drewhirschi/daily_mirror/docs/drews-convo-with-claude-9.16.26.md

Can an esp 32 p4 run a light web server

Yes, easily. The ESP32-P4 has a dual-core RISC-V at up to 400MHz with plenty of RAM (768KB HP SRAM, plus optional PSRAM), so running a lightweight HTTP server is well within its capabilities — you could run ESP-IDF's esp_http_server component, or something like Mongoose, and serve a decent number of concurrent connections for typical IoT/local-network use cases.

One thing worth flagging: the P4 itself has no built-in WiFi or Bluetooth. Espressif paired it with the ESP32-C6 as a companion chip (communicating over SDIO) to provide connectivity — that's the setup used on the ESP32-P4 Function EV boards. So if you want the web server reachable over WiFi, you'll be using the P4 for compute and the C6 for the radio, coordinated over ESP-Hosted or a similar bridge.

If you just need Ethernet instead, the P4 has native support for that (RMII), which simplifies things since you skip the companion-chip dance entirely.

How easy would it be to write that in rust

Recalled memory
Recalled memory
Moderately easy, but with a caveat specific to the P4: it's RISC-V, and RISC-V support in the Rust ESP ecosystem is more mature than the Xtensa side, so you're actually in a better position here than you'd be on an S3 or S2.

The realistic paths:

esp-hal (no_std) + Embassy — async runtime, and someone's likely already got esp_http_server-equivalent examples or you'd wire up a minimal HTTP parser yourself over embassy-net. This is the "real embedded Rust" path: no allocator dependency by default, smaller footprint, but you're writing more of the HTTP layer yourself since the ecosystem's web server crates aren't as batteries-included as esp_http_server in C.
esp-idf-hal / esp-idf-svc (std) — Rust on top of ESP-IDF, giving you std, an allocator, threads, and direct bindings to ESP-IDF's own esp_http_server. This is the pragmatic choice if you want something working quickly: you get IDF's HTTP server for free via Rust bindings instead of hand-rolling it, at the cost of pulling in the full IDF toolchain and being less "pure Rust embedded."
Given you'd want a web server running soon rather than as a learning exercise in async embedded networking, esp-idf-svc is the faster route — it's essentially the C setup with a Rust face on it. The esp-hal/Embassy route is more idiomatic and lighter-weight but means more plumbing, especially since you'd also need to handle the P4/C6 companion-chip networking split at a lower level than IDF's WiFi abstraction handles it for you.

Worth checking current esp-hal P4 support status before committing — RISC-V support has been moving fast but P4-specific peripheral coverage (particularly around the SDIO link to the C6) may still have gaps compared to S3.

What can the c6 do as far as running a camera?

Thought for 4s
Thought for 4s
Not much, camera-wise — and this matters for how you'd architect it.

The ESP32-C6 is a connectivity-only chip: single-core RISC-V, WiFi 6, Bluetooth 5, and 802.15.4 (Thread/Zigbee). It has no DVP or MIPI-CSI camera interface at all. In the P4+C6 pairing, the C6's whole job is radio — it talks to the P4 over SDIO (via ESP-Hosted) purely to give the P4 WiFi/BT, nothing else.

Camera capture stays entirely on the P4 side. The P4 actually has solid camera support built in — both a DVP parallel interface (like the older S2/S3 camera setups) and a MIPI-CSI-2 interface, which is new for the ESP32 line and lets you use higher-resolution MIPI camera modules (like some Raspberry Pi camera sensors use) rather than being stuck with DVP-only sensors like the OV2640/OV5640 that dominate the ESP32-CAM world.

So for a P4-based camera project: P4 handles image capture and processing (and could run the ISP pipeline if you're using the CSI path), C6 just gets the resulting frames onto the network. That's a meaningfully different pipeline than the ESP32-S3 setups you'd been looking at, where the same chip does both — worth keeping in mind if you're weighing it against the S3/Arducam Mega path.

Could the c6 own its own stream raw sensor data to a backend?

No — the C6 has no camera interface (no DVP, no MIPI-CSI), so it physically can't connect to an image sensor to pull raw frame data off it. Camera sensors need those parallel/serial video interfaces to hand off pixel data at usable rates; you can't get there over the C6's available buses.

The only way raw sensor data would reach the C6 is if the P4 captures it and hands it over — at which point the C6 is just relaying data, not sourcing it. Options in that vein:

P4 captures → passes raw/compressed frames to C6 over SDIO → C6 streams to backend over WiFi. This is basically what ESP-Hosted already does implicitly for networking, but you could also treat it as an explicit data pipe if you wanted the P4 doing zero network-stack work itself, just handing frame buffers across.
P4 does everything, including WiFi via the C6 driver stack. This is the "normal" ESP-Hosted setup — C6 is invisible as a distinct actor, it's just the radio backend for the P4's network calls. Simpler, since you're not building your own inter-chip data protocol.
If you're aiming for something like "sensor talks directly to the radio chip, P4 does no camera work at all," that's not achievable on this pairing — there's no independent sensor→C6 path. The P4 has to be in the loop for capture no matter what, since it's the only chip with a camera interface.

Forget P4, what other esp32s should we look into?

Thought for 18s
Thought for 18s
You're mostly right, with one correction that matters for how you use the film.

Used the browser (7 actions) · 3 notes

Used the browser (7 actions) · 3 notes
like what do lcd panels use to even out light

Clicked, waited, opened +1
Clicked, waited, opened +1
Cart's whole again — all 9 items, and I re-added the three that silently dropped. Now your question, which is a better one than the film-vs-channel debate.

What LCDs actually do
The diffuser sheet isn't the part doing the work. The real trick is the light guide plate (LGP): a clear acrylic sheet with the LEDs firing into its edge, not its face. Light bounces along inside by total internal reflection, and a printed or etched dot pattern on the back kicks it out toward the viewer. The dots get progressively denser the farther you are from the LED edge, which is what cancels the falloff and makes the whole face read as uniform.

The full stack, back to front:

White reflector — bounces escaping light back in
Light guide plate — the even-ing happens here
Diffuser sheet — cleans up any residual dot structure
Prism film (BEF), often two layers crossed at 90° — redirects off-axis light forward, recovering a big chunk of brightness
DBEF reflective polarizer — recycles the polarization the LCD would have thrown away
That's why a phone screen is 2mm thick and perfectly even, while your strip-behind-film needs a 10–20mm air gap to look decent. Edge-lighting sidesteps the gap entirely.

Why this matters for your build
This is directly applicable, and it's arguably a better design than the ring:

Fire your COB strips into the edges of a 7×7 acrylic sheet, not at the subject. White reflector behind, diffuser on the front. You get a 7×7 panel that glows across its whole face instead of a 7×7 outline.

Same apparent width as the ring, so same softness — but roughly 3× the emitting area, so more usable light, and the reflection in glasses becomes a large dim rectangle rather than a bright thin ring. Large-and-dim is the more forgiving failure mode.

At 7 inches, you don't need a real engineered LGP. The dot-density gradient exists because a 27″ monitor has to push light a long way. Over 3.5″ from each edge, plain frosted/opal acrylic edge-lit will glow acceptably evenly — the physics is forgiving at this scale. Light-diffusing acrylic ("sign white," 32–43% transmission) edge-lit from all four sides is probably all you need.

The free version: gut a dead LCD monitor or laptop. You get the LGP, diffuser sheets, BEF, and reflector as a matched stack, already cut flat, for nothing. Even if you don't use the LGP itself, the prism film is the part you can't easily buy in small quantities and it's a genuine brightness multiplier. If you have any dead panel around, that's worth an hour with a screwdriver before buying anything.

On the rails vs. film question
You were right that the channel isn't necessary, and for a flash-duty build the heatsink argument mostly evaporates — 10W for under a second doesn't need aluminum. But the savings are small ($20 vs $15); the actual reason to skip it is that it locks you into one geometry before you know what you want.

I left the Muzata in the cart rather than pulling it, since the edge-lit approach might change what you need entirely. Say the word and I'll remove it. The diffusion gel is worth keeping either way — it's how you'll test stack density cheaply, whichever direction you go.

This conversation has moved to a view that isn’t available here.

Write a message…

Claude is AI and can make mistakes. Please double-check responses.
There was a problem displaying content from visualize.
