drewhirschi/daily_mirror/hardware/enclosure-v2/viewer-template.html

DAILY MIRROR / PROTOTYPE 02

# Enclosure + adjustable rail

Drag to orbit. Scroll to zoom. Explore the actual CAD geometry without FreeCAD.

Your browser needs WebGL to display this model.

140 × 170 × 55 mm enclosure (5.5 × 6.7 × 2.2 in) · 300 mm travel

View Height above lowest position: 146 mm Separate front panel: 0 mm

Electronics envelopesFuture flash spaceReset view

Rail and housing

Carriage, knob and end stops

Pi and camera references

The front panel carries the camera, LED and button. The entire enclosure slides together, so only the external power cable needs a service loop. Tightening the knob presses a small brake pad against the rail.

CAD geometry checked. Camera lens, controls, printer fit, friction and holding load still need a physical trial. Amber flash space is a future allowance.

Download print pack · Assembly and printing guide · FreeCAD model · Assembly STEP
