drewhirschi/daily_mirror/firmware/esp-idf/main/mirror_press.c

#include <string.h>

#include "mirror_press.h"
#include "mirror_pair.h"
#include "mirror_ring.h"
#include "mirror_upload.h"
#include "mirror_spool.h"
#include "mirror_board.h"

#include "freertos/FreeRTOS.h"
#include "freertos/task.h"
#include "freertos/semphr.h"
#include "esp_log.h"
#include "esp_heap_caps.h"
#include "esp_timer.h"
#include <inttypes.h>
#include "driver/gpio.h"

static const char *TAG = "mirror_press";

/* Same numbers as the Pi (device/src/main.rs): a 60 ms settle is long enough
 * for these switches and short enough that the press still feels immediate,
 * and a 20 ms poll costs nothing next to it. */
#define DEBOUNCE_MS 60
#define POLL_MS     20

/* The gesture thresholds, from crates/mirror-core/src/lib.rs `timing`. The
 * detector below is a port of crates/mirror-core/src/button.rs, so the same
 * hold feels the same on the Pi, in the host tests and here. */
#define HOLD_ARM_MS           2000   /* the ring starts filling amber */
#define HOLD_PAIR_MS          5000   /* enter pairing */
#define HOLD_RESET_MS        20000   /* the full reset becomes armed */
#define RESET_CLICK_WINDOW_MS 3000   /* clicks must land inside this */
#define RESET_CLICK_COUNT        3

static uint8_t *s_last_jpg;         /* the committed photo, in PSRAM */
static size_t s_last_len;
static SemaphoreHandle_t s_last_lock;
static volatile bool s_busy;
static volatile uint32_t s_count;

bool mirror_press_busy(void)     { return s_busy; }
uint32_t mirror_press_count(void) { return s_count; }

bool mirror_press_last_acquire(const uint8_t **jpeg, size_t *len)
{
    if (!s_last_lock) {
        return false;
    }
    xSemaphoreTake(s_last_lock, portMAX_DELAY);
    if (!s_last_jpg || !s_last_len) {
        xSemaphoreGive(s_last_lock);
        return false;
    }
    *jpeg = s_last_jpg;
    *len = s_last_len;
    return true;
}

void mirror_press_last_release(void)
{
    if (s_last_lock) {
        xSemaphoreGive(s_last_lock);
    }
}

/* Copy into the slot. This is the commit point: once it returns true the
 * photo survives the camera buffer going back to the driver, and a later
 * upload failure cannot lose it. */
static bool commit(const uint8_t *jpeg, size_t len)
{
    uint8_t *copy = heap_caps_malloc(len, MALLOC_CAP_SPIRAM | MALLOC_CAP_8BIT);
    if (!copy) {
        ESP_LOGE(TAG, "no PSRAM for a %u byte photo", (unsigned)len);
        return false;
    }
    memcpy(copy, jpeg, len);
    xSemaphoreTake(s_last_lock, portMAX_DELAY);
    free(s_last_jpg);
    s_last_jpg = copy;
    s_last_len = len;
    xSemaphoreGive(s_last_lock);
    return true;
}

/* Sleep until `ms` after `started`, or return at once if that is already past. */
static void wait_until(int64_t started, uint32_t ms)
{
    int64_t elapsed = (esp_timer_get_time() - started) / 1000;
    if (elapsed < (int64_t)ms) {
        vTaskDelay(pdMS_TO_TICKS((uint32_t)(ms - elapsed)));
    }
}

static esp_timer_handle_t s_flash_timer;

static void flash_on_cb(void *arg)
{
    (void)arg;
    board_flash_set(true);
}

/* Turn the flash on `ms` into the countdown, whatever this task is doing. */
static void arm_flash_at(uint32_t ms)
{
    if (!s_flash_timer) {
        const esp_timer_create_args_t args = {
            .callback = flash_on_cb, .name = "flash_on",
        };
        if (esp_timer_create(&args, &s_flash_timer) != ESP_OK) {
            return;
        }
    }
    esp_timer_stop(s_flash_timer);
    esp_timer_start_once(s_flash_timer, (uint64_t)ms * 1000);
}

static uint32_t flash_lead_ms(void)
{
    if (!board_flash_available()) {
        return 0;
    }
    uint32_t lead = CONFIG_MIRROR_FLASH_LEAD_MS;
    /* Never longer than the countdown it has to fit inside. */
    return lead > MIRROR_RING_COUNTDOWN_MS - 300 ? MIRROR_RING_COUNTDOWN_MS - 300 : lead;
}
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
